sorchard001/D32MKII-Schematic/Dragon32_MKII.kicad_sch

## KiCad design Dragon32_MKII.kicad_sch (2026-08-14)

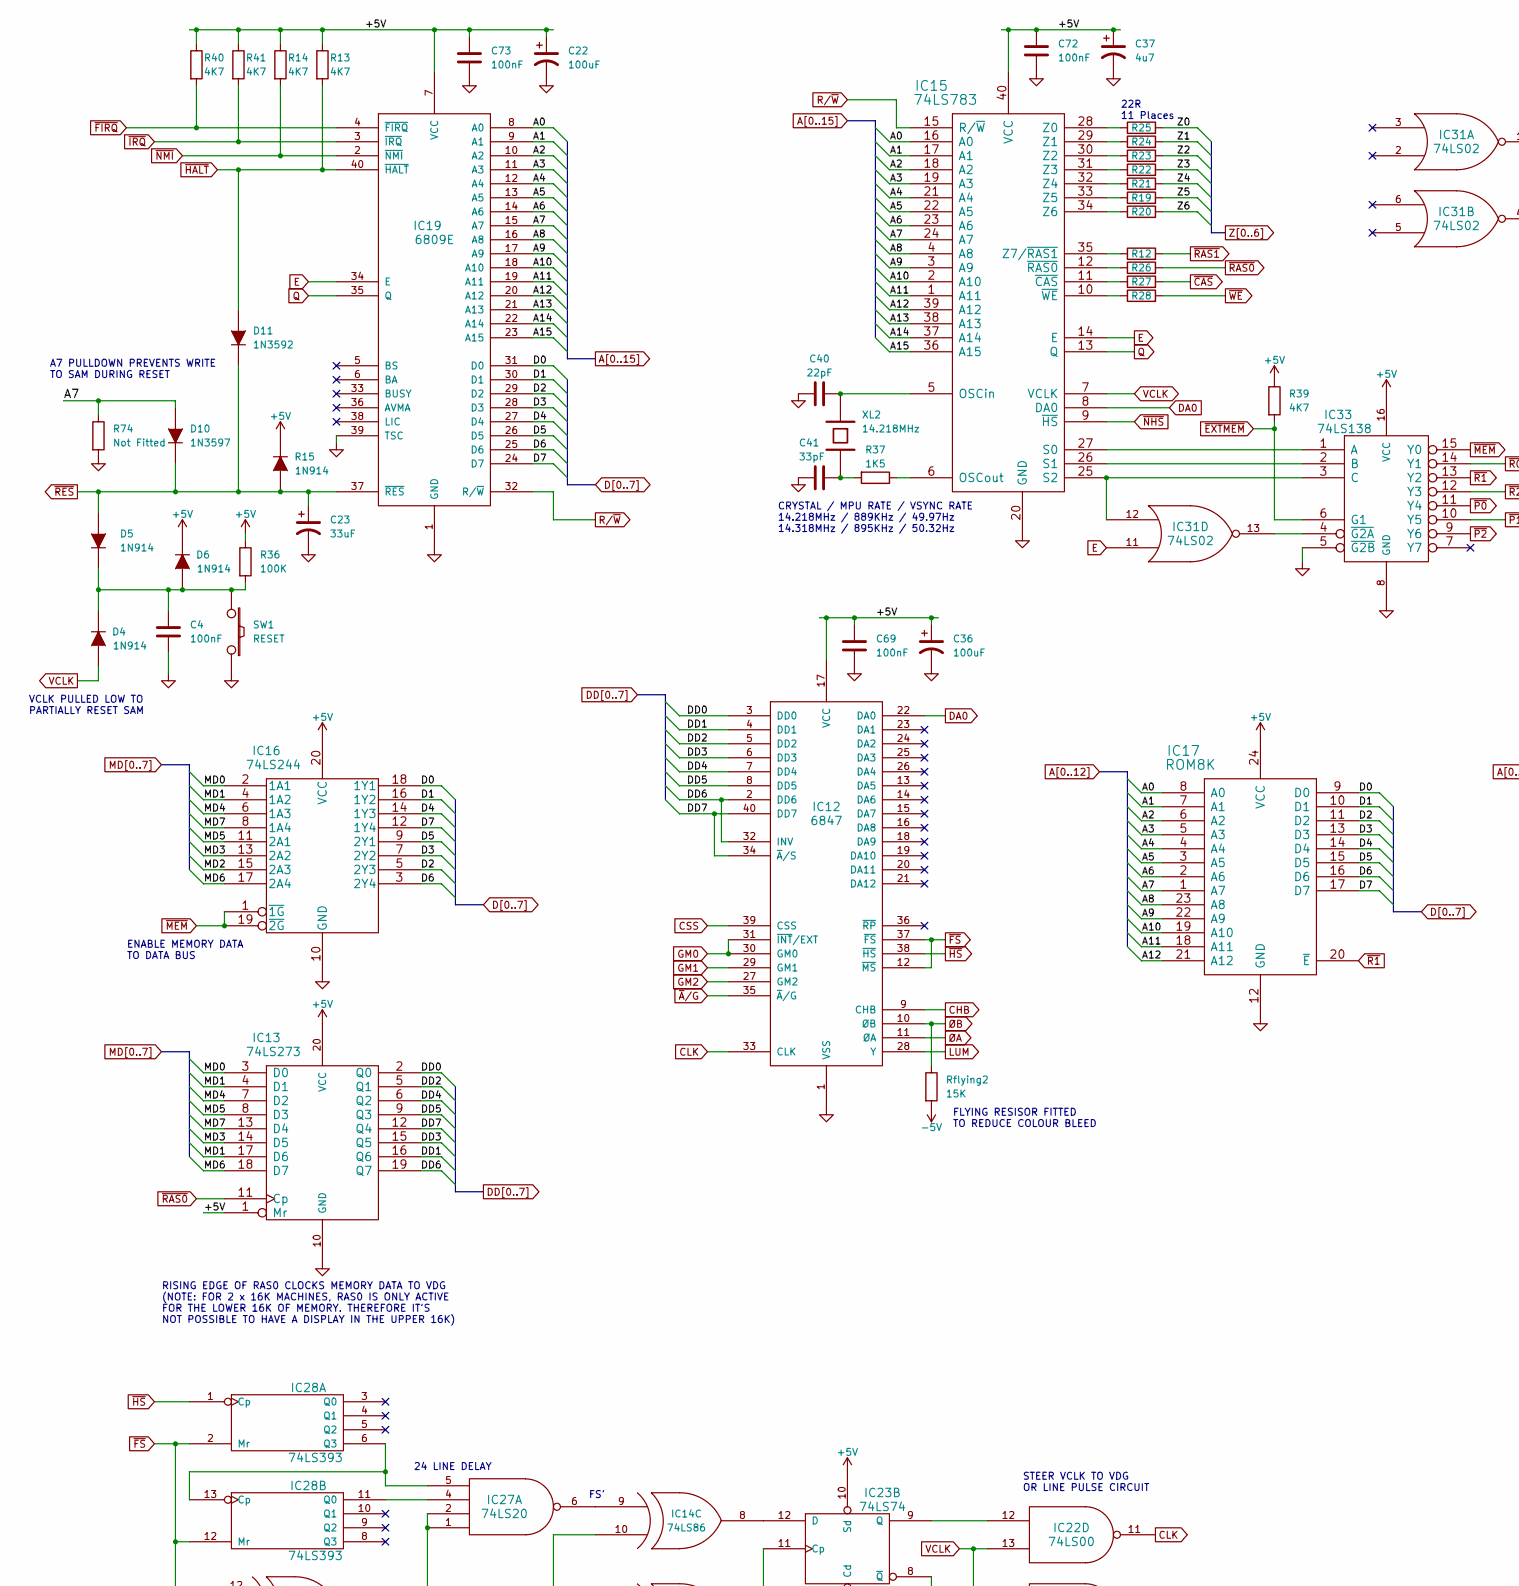
[picture p2: schematic Dragon32_MKII.kicad_sch, part in row 1, column 1]

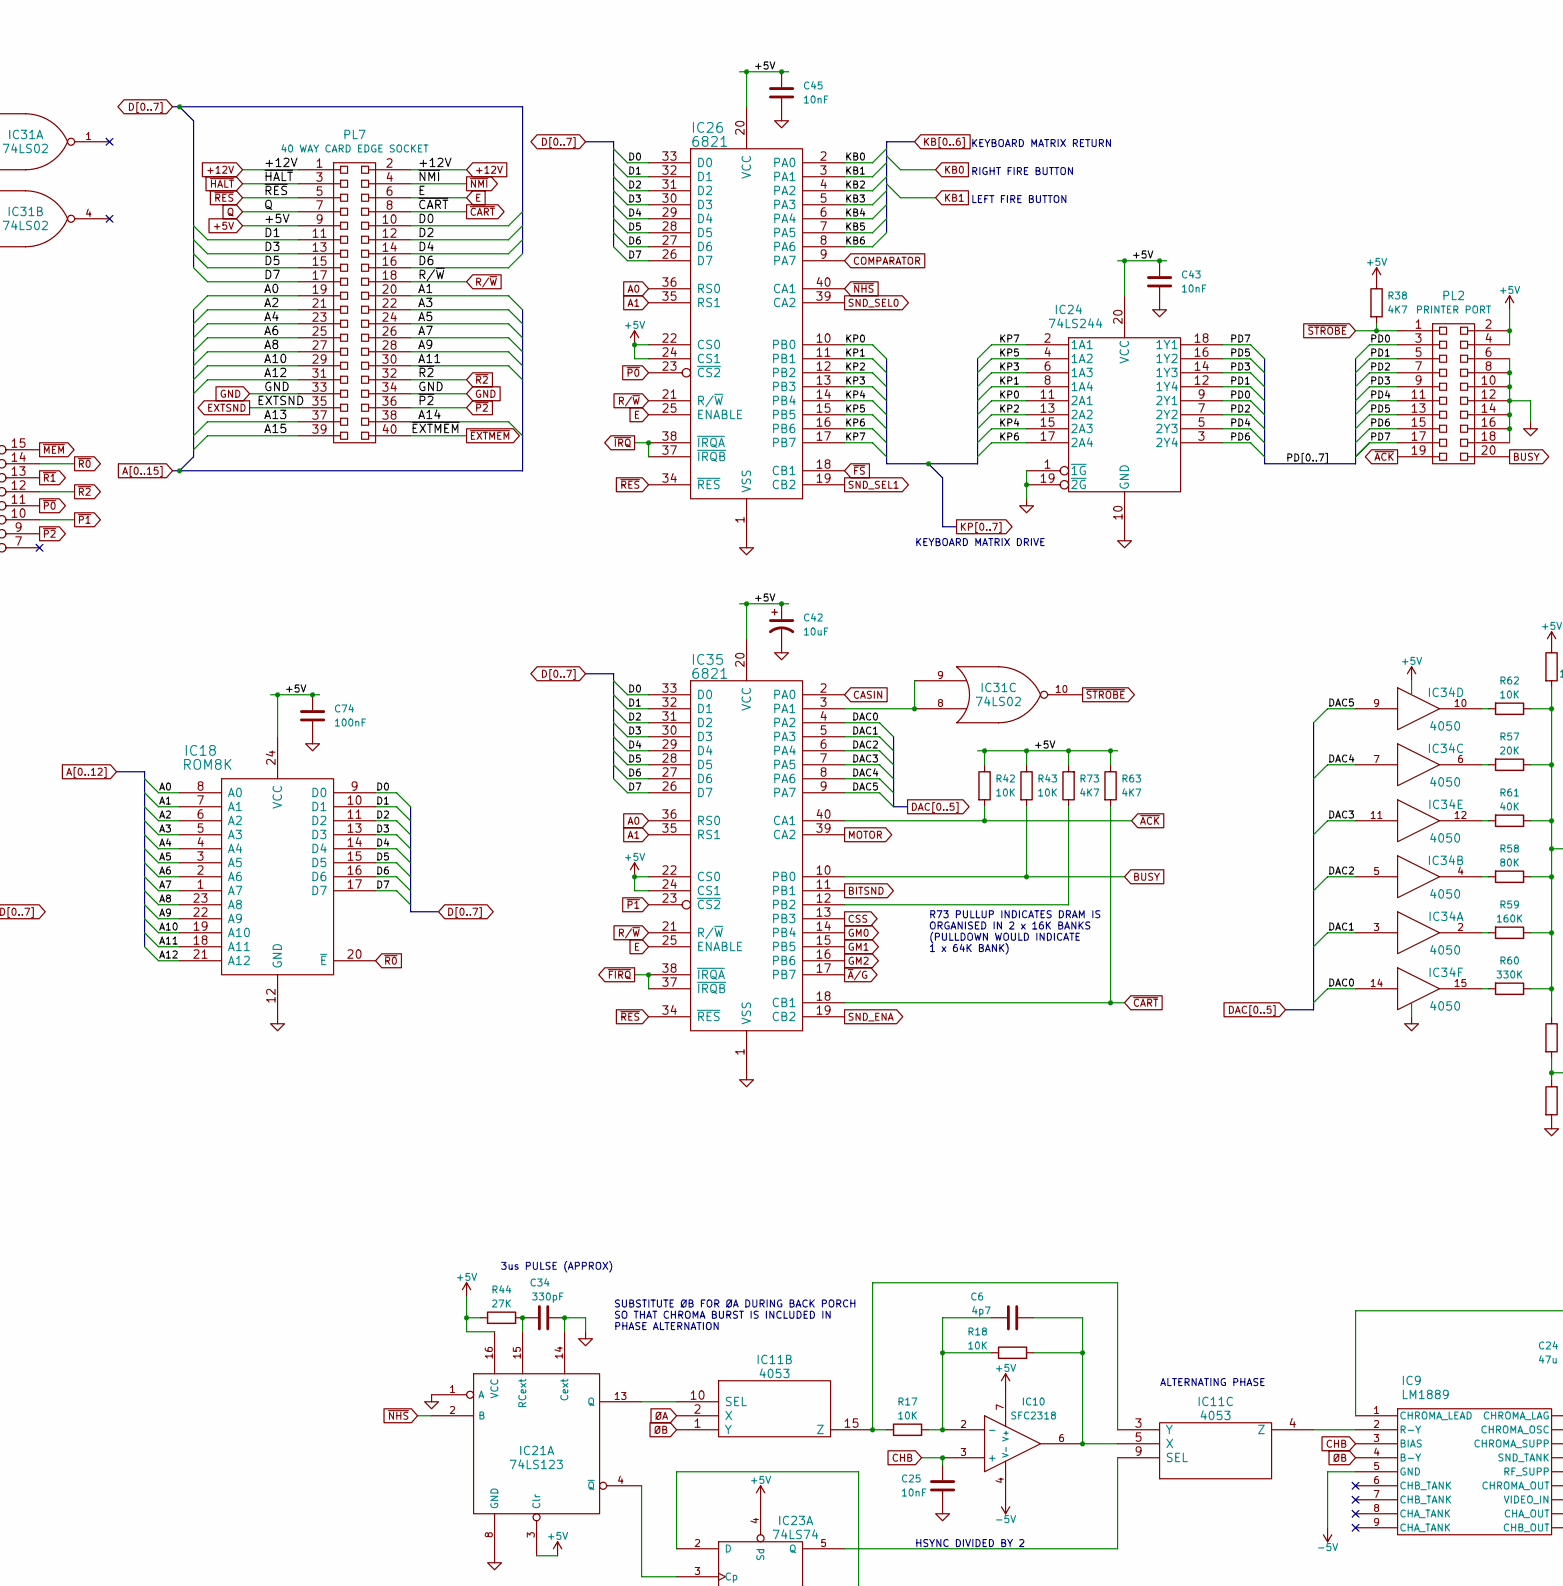
[picture p3: schematic Dragon32_MKII.kicad_sch, part in row 1, column 2]

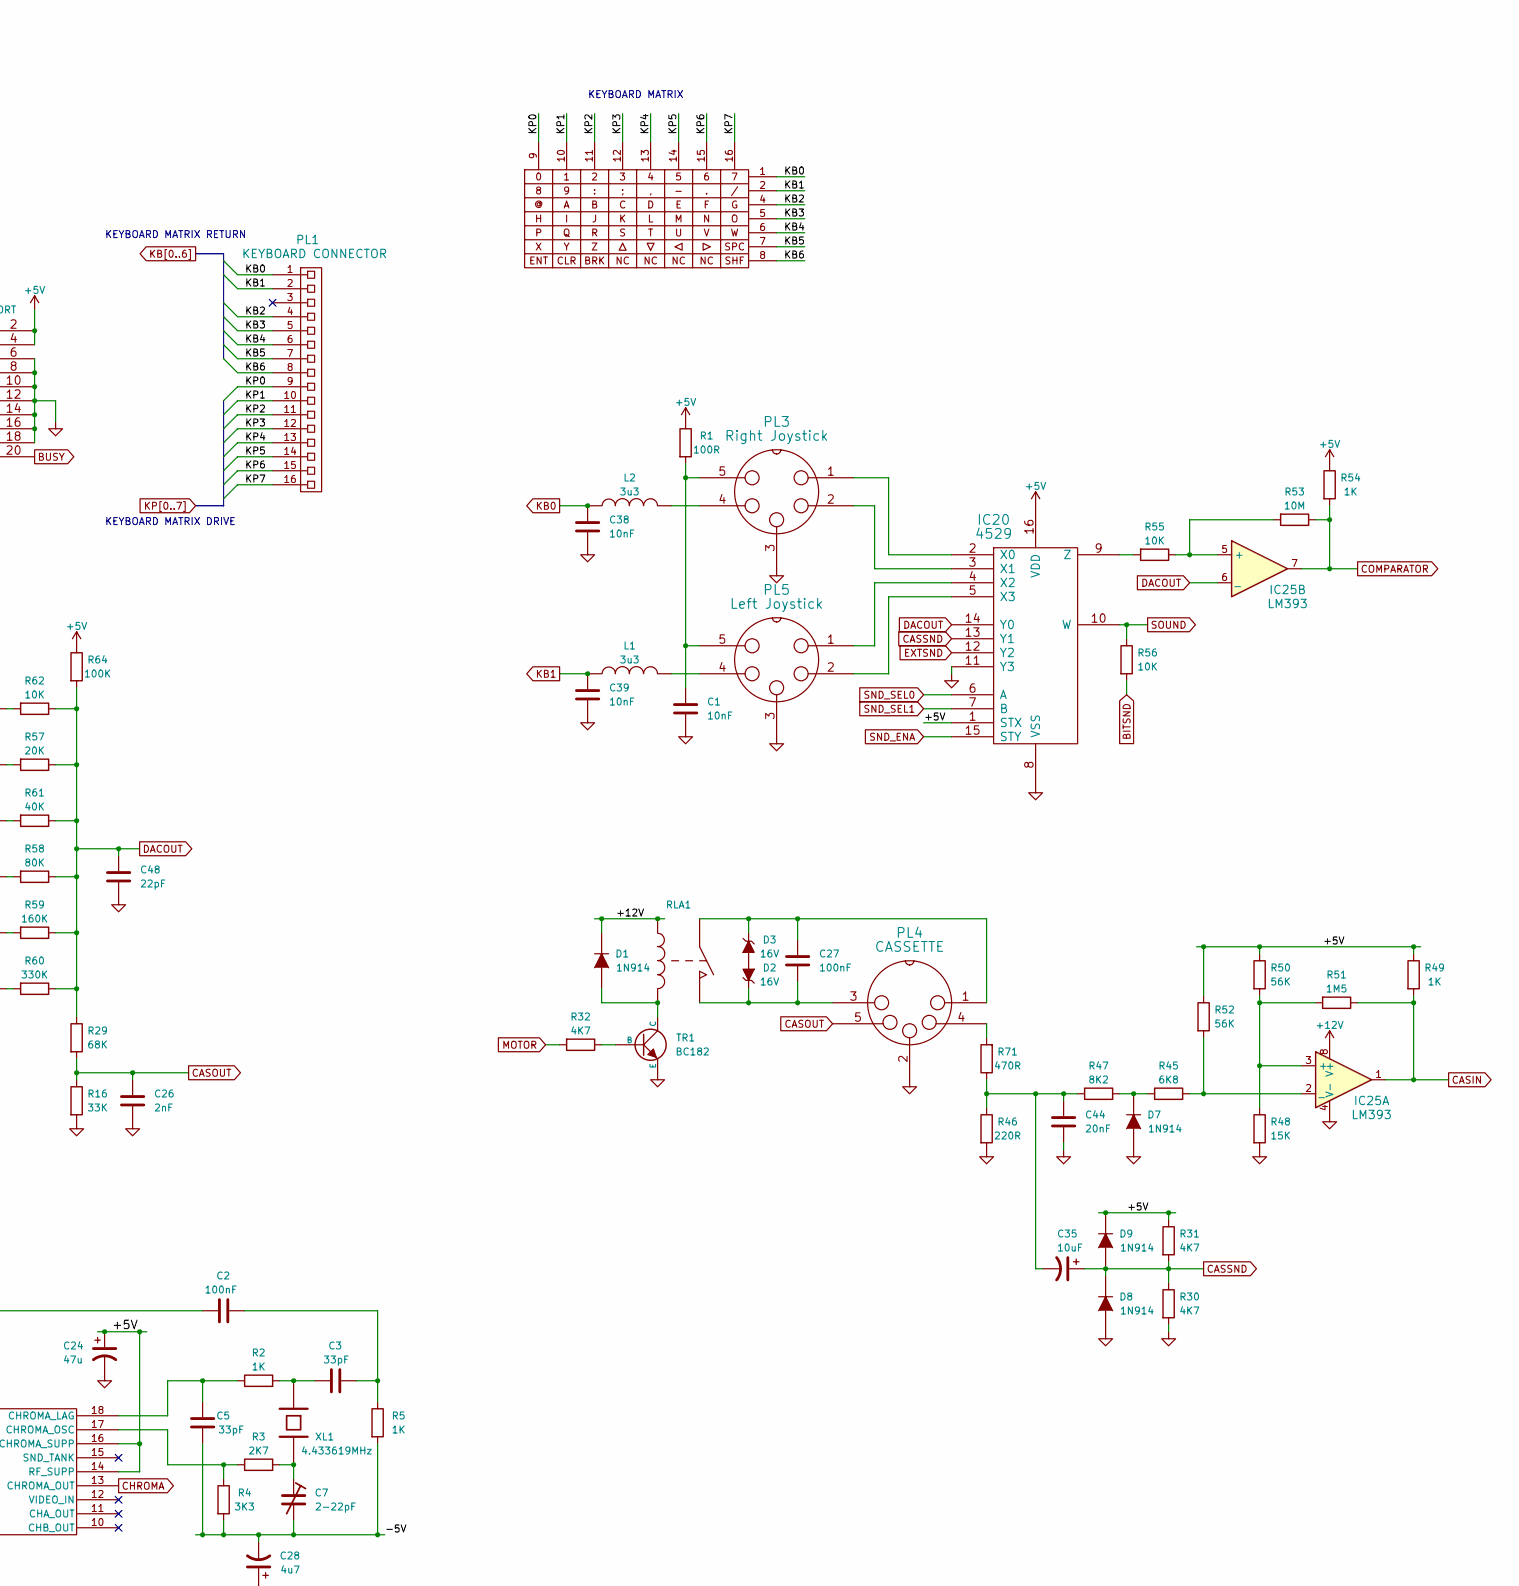
[picture p4: schematic Dragon32_MKII.kicad_sch, part in row 1, column 3]

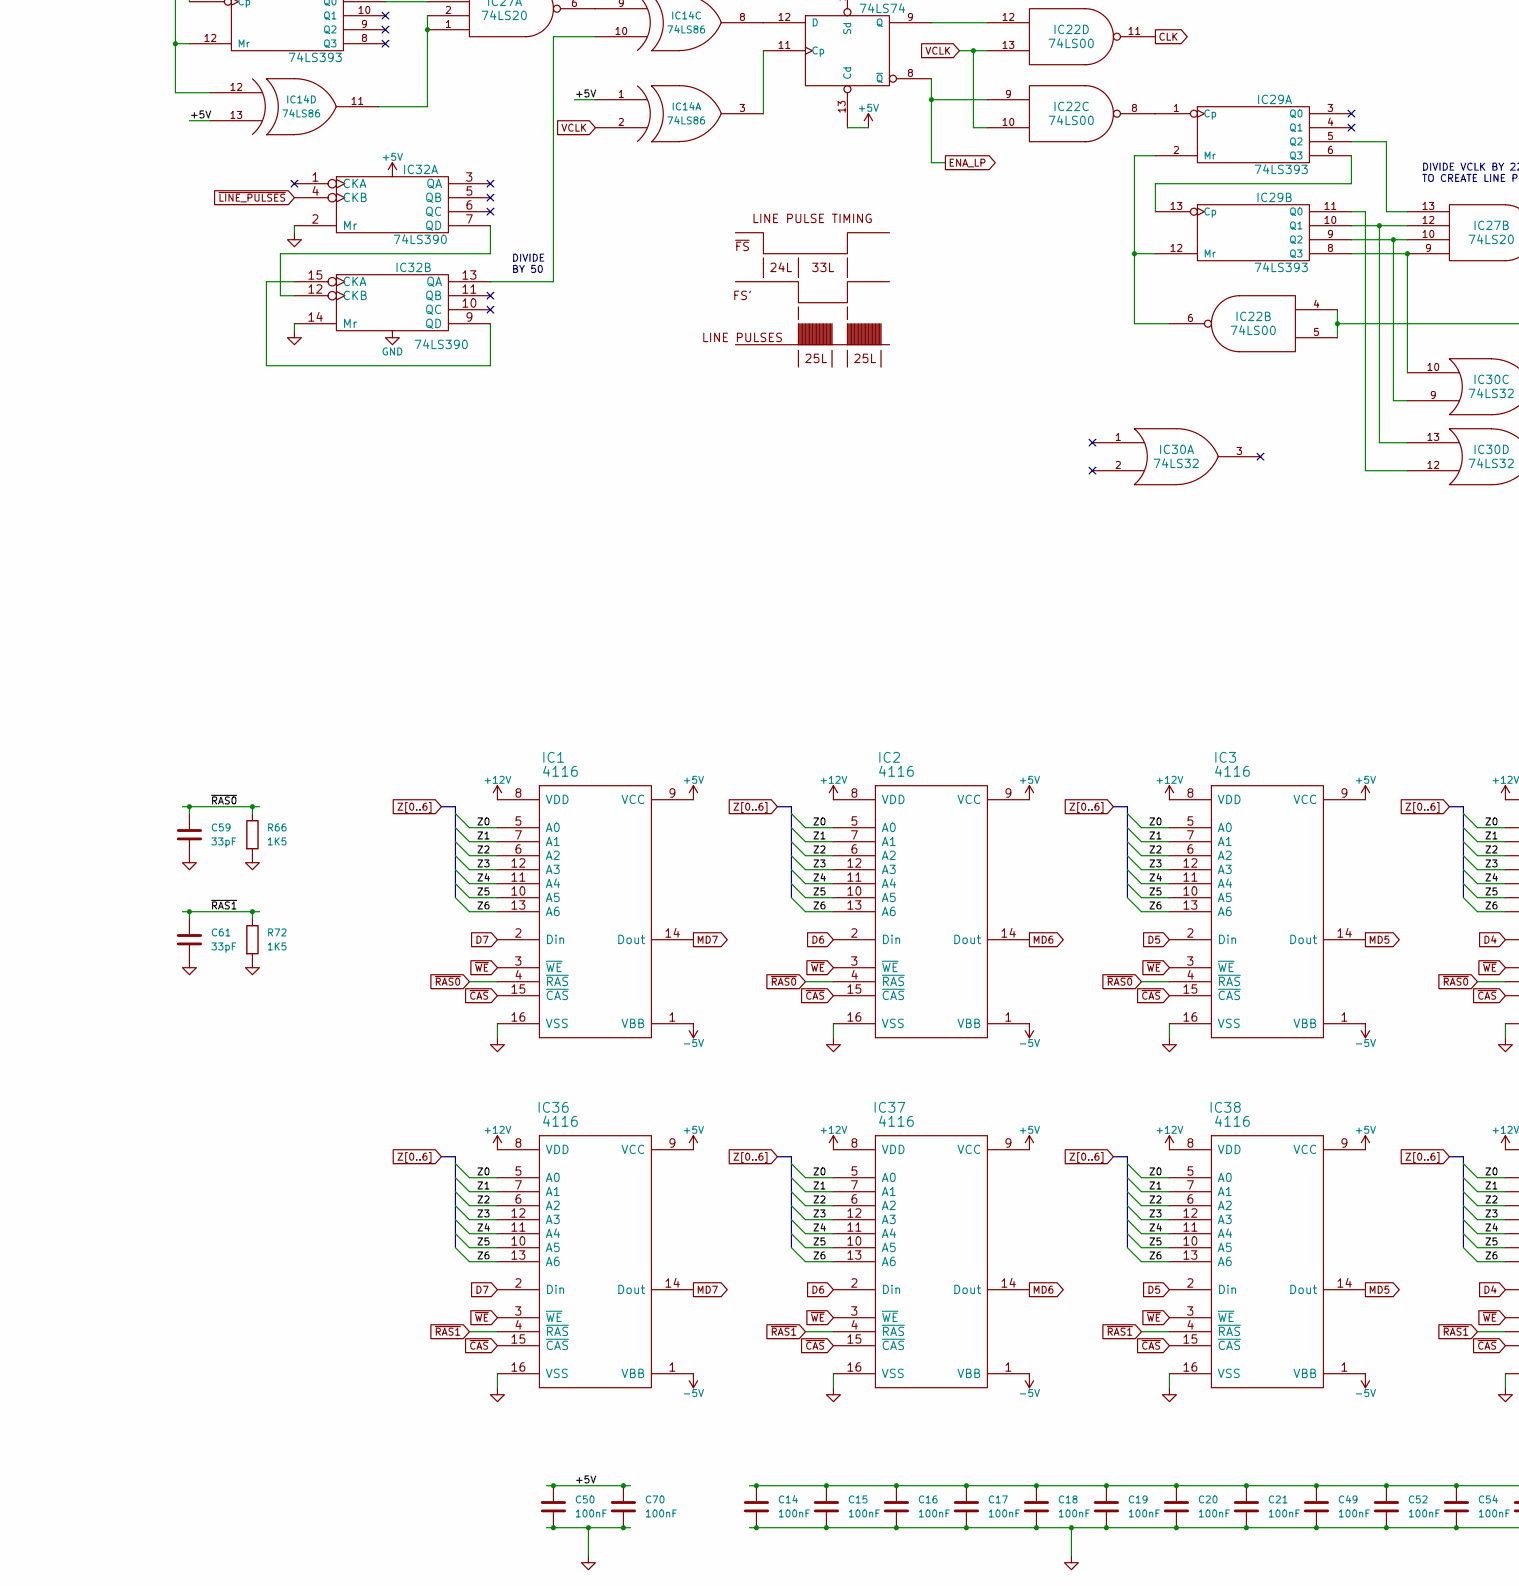
[picture p5: schematic Dragon32_MKII.kicad_sch, part in row 2, column 1]

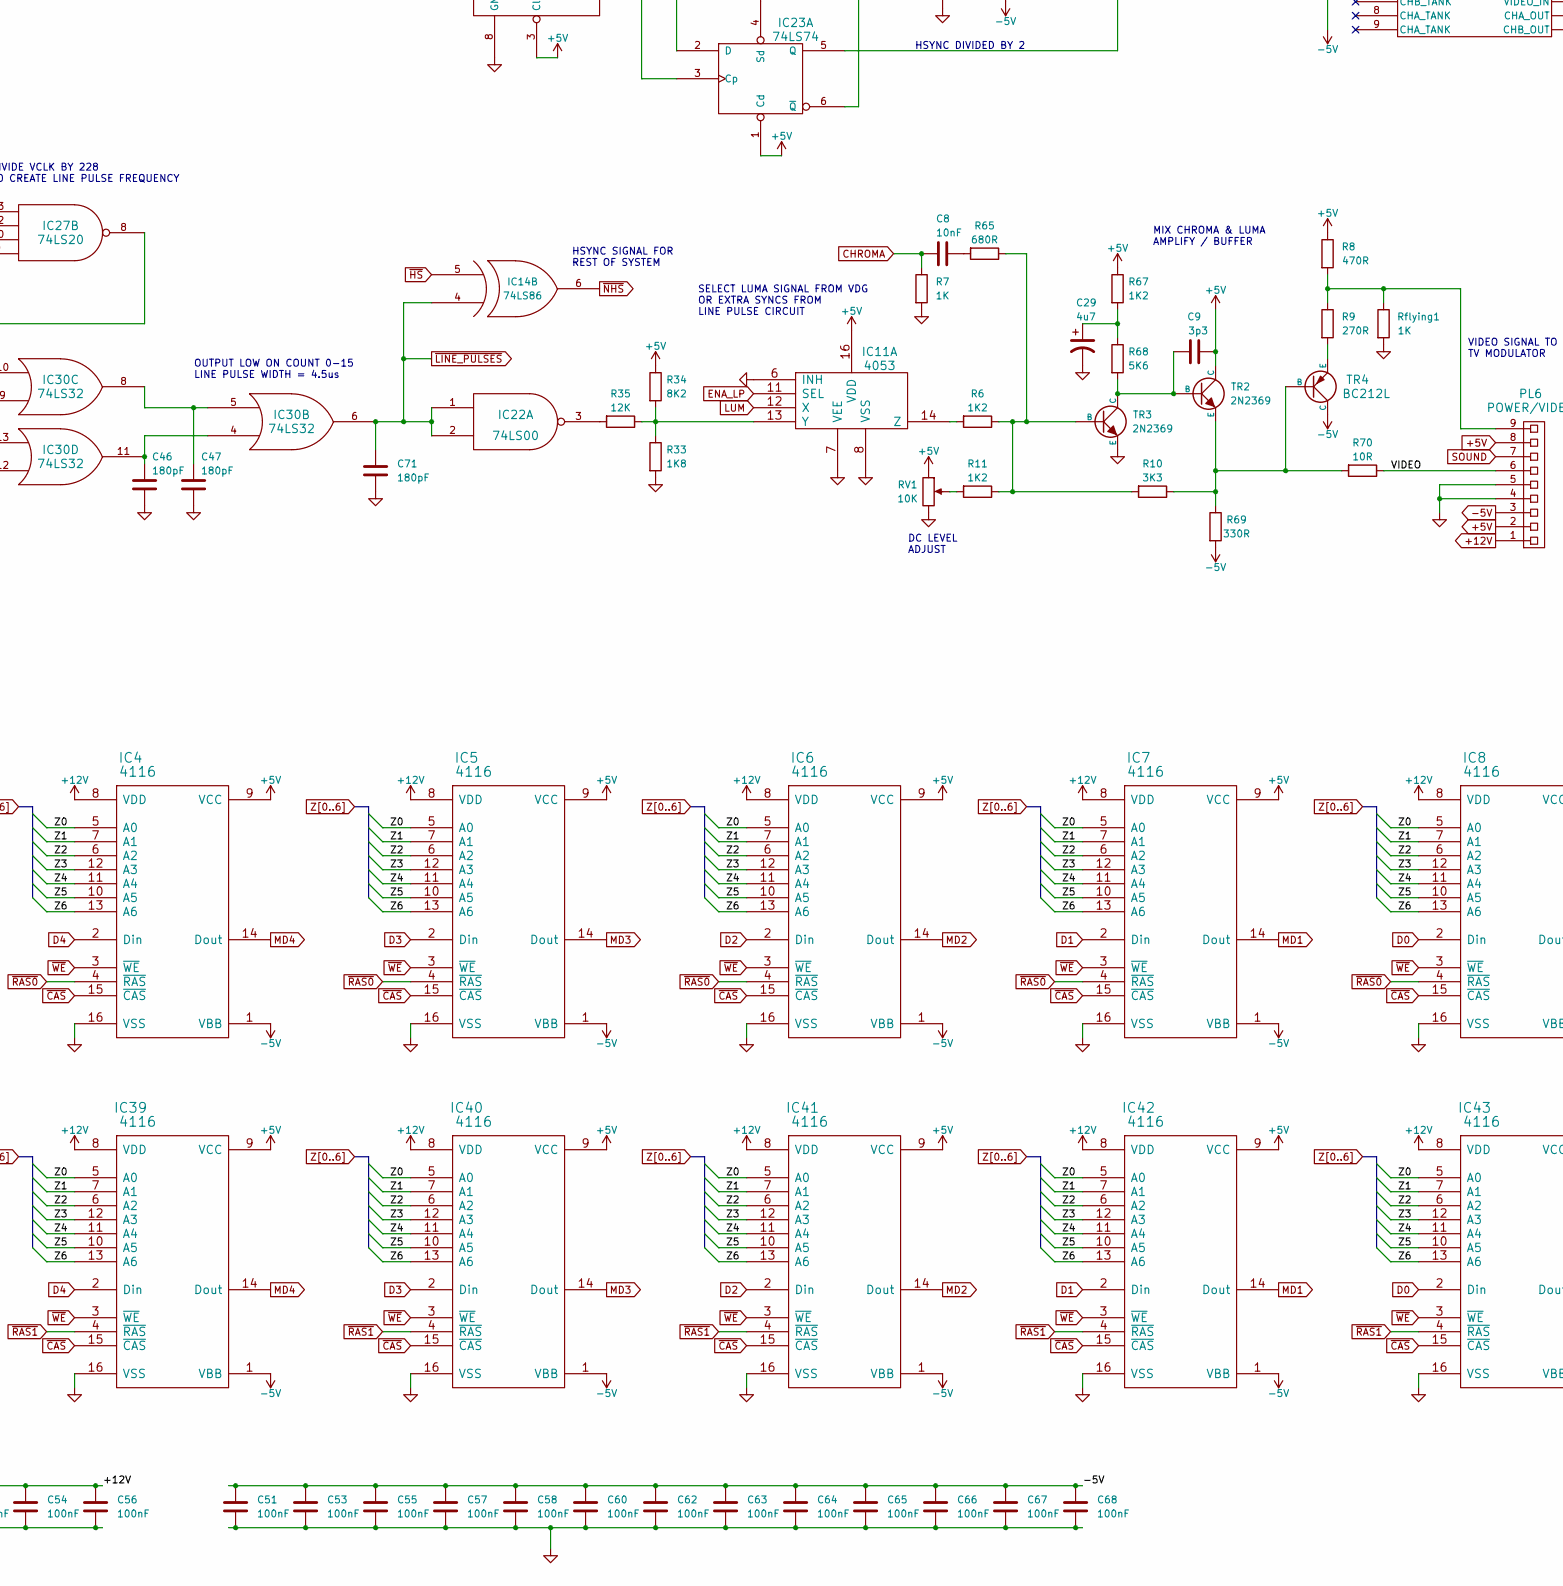
[picture p6: schematic Dragon32_MKII.kicad_sch, part in row 2, column 2]

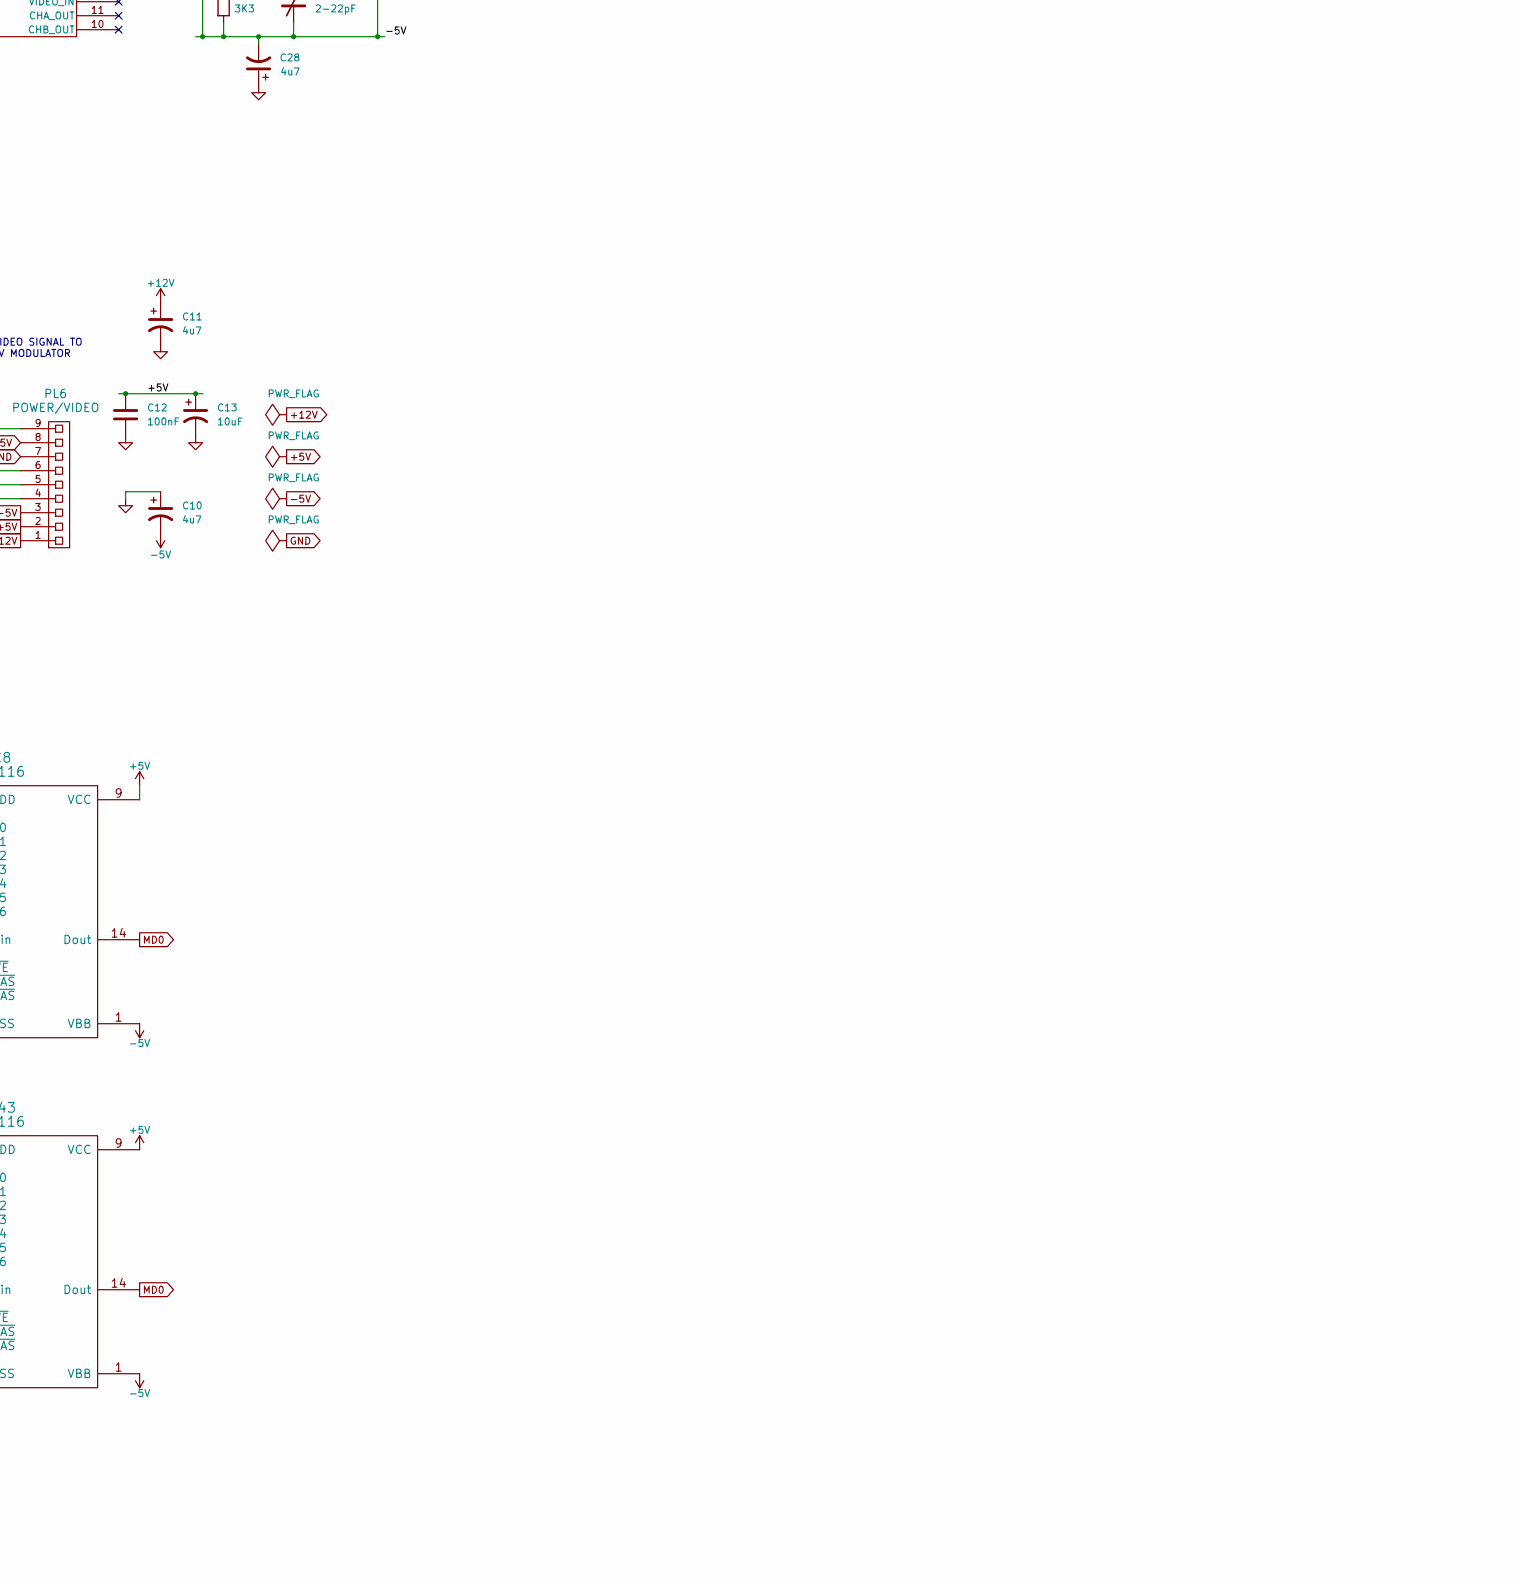
[picture p7: schematic Dragon32_MKII.kicad_sch, part in row 2, column 3]

Parts:
C1, C8, C25, C38, C39, C43, C45: 10nF
C2, C4, C12, C14, C15, C16, C17, C18, C19, C20, C21, C27, C49, C50, C51, C52, C53, C54, C55, C56, C57, C58, C60, C62, C63, C64, C65, C66, C67, C68, C69, C70, C72, C73, C74: 100nF
C3, C5, C41, C59, C61: 33pF
C6: 4p7
C7: 2-22pF
C9: 3p3
C10, C11, C28, C29, C37: 4u7
C13, C35, C42: 10uF
C22, C36: 100uF
C23: 33uF
C24: 47u
C26: 2nF
C34: 330pF
C40, C48: 22pF
C44: 20nF
C46, C47, C71: 180pF
D1, D4, D5, D6, D7, D8, D9: 1N914
D2, D3: 16V
D10: 1N3597
D11: 1N3592
IC1, IC2, IC3, IC4, IC5, IC6, IC7, IC8, IC36, IC37, IC38, IC39, IC40, IC41, IC42, IC43: 4116
IC9: LM1889
IC10: SFC2318
IC11: 4053
IC12: 6847
IC13: 74LS273
IC14: 74LS86
IC15: 74LS783
IC16, IC24: 74LS244
IC17, IC18: ROM8K
IC19: 6809E
IC20: 4529
IC21: 74LS123
IC22: 74LS00
IC23: 74LS74
IC25: LM393
IC26, IC35: 6821
IC27: 74LS20
IC28, IC29: 74LS393
IC30: 74LS32
IC31: 74LS02
IC32: 74LS390
IC33: 74LS138
IC34: 4050
L1, L2: 3u3
PL1: KEYBOARD CONNECTOR
PL2: PRINTER PORT
PL3: Right Joystick
PL4: CASSETTE
PL5: Left Joystick
PL6: POWER/VIDEO
PL7: 40 WAY CARD EDGE SOCKET
R1: 100R
R2, R5, R7, R49, R54: 1K
R3: 2K7
R4, R10: 3K3
R6, R11, R67: 1K2
R8, R71: 470R
R9: 270R
R12, R19, R20, R21, R22, R23, R24, R25, R26, R27, R28: 22R
R13, R14, R30, R31, R32, R38, R39, R40, R41, R63, R73: 4K7
R15: 1N914
R16: 33K
R17, R18, R42, R43, R55, R56, R62: 10K
R29: 68K
R33: 1K8
R34, R47: 8K2
R35: 12K
R36, R64: 100K
R37, R66, R72: 1K5
R44: 27K
R45: 6K8
R46: 220R
R48: 15K
R50, R52: 56K
R51: 1M5
R53: 10M
R57: 20K
R58: 80K
R59: 160K
R60: 330K
R61: 40K
R65: 680R
R68: 5K6
R69: 330R
R70: 10R
R74: Not Fitted
RLA1: RELAY
RV1: 10K
Rflying1: 1K
Rflying2: 15K
SW1: RESET
TR1: BC182; TO92-CBE
TR2, TR3: 2N2369
TR4: BC212L
U1: LINE_PULSE_DIAGRAM
U2: (no value)
XL1: 4.433619MHz
XL2: 14.218MHz

Connections:
+5V: C9.2, C12.1, C13.1, C22.1, C24.1, C36.1, C37.1, C42.1, C43.1, C45.1, C50.1, C69.1, C70.1, C72.1, C73.1, C74.1, D6.2 (K), D9.2 (K), IC1.9 (VCC), IC2.9 (VCC), IC3.9 (VCC), IC4.9 (VCC), IC5.9 (VCC), IC6.9 (VCC), IC7.9 (VCC), IC8.9 (VCC), IC9.14 (RF_SUPP), IC9.16 (CHROMA_SUPP), IC10.7 (V+), IC11.16 (VDD), IC12.17 (VCC), IC13.1 (Mr), IC13.20 (VCC), IC14.1 (IN1), IC14.13 (IN2), IC15.40 (VCC), IC16.20 (VCC), IC17.24 (VCC), IC18.24 (VCC), IC19.7 (VCC), IC20.1 (STX), IC20.16 (VDD), IC21.3 (Clr), IC21.16 (VCC), IC23.1 (Cd), IC23.4 (Sd), IC23.10 (Sd), IC23.13 (Cd), IC24.20 (VCC), IC26.20 (VCC), IC26.22 (CS0), IC26.24 (CS1), IC32.16 (VCC), IC33.16 (VCC), IC34.1 (VCC), IC35.20 (VCC), IC35.22 (CS0), IC35.24 (CS1), IC36.9 (VCC), IC37.9 (VCC), IC38.9 (VCC), IC39.9 (VCC), IC40.9 (VCC), IC41.9 (VCC), IC42.9 (VCC), IC43.9 (VCC), PL2.2, PL2.4, PL6.2, PL6.8, PL7.9, R1.1, R8.1, R13.1, R14.1, R15.2 (K), R31.1, R34.1, R36.1, R38.1, R39.1, R40.1, R41.1, R42.1, R43.1, R44.1, R49.1, R50.1, R52.1, R54.1, R63.1, R64.1, R67.1, R73.2, RV1.1, TR2.3 (C)
+12V: C11.1, C14.1, C15.1, C16.1, C17.1, C18.1, C19.1, C20.1, C21.1, C49.1, C52.1, C54.1, C56.1, D1.2 (K), IC1.8 (VDD), IC2.8 (VDD), IC3.8 (VDD), IC4.8 (VDD), IC5.8 (VDD), IC6.8 (VDD), IC7.8 (VDD), IC8.8 (VDD), IC25.8 (V+), IC36.8 (VDD), IC37.8 (VDD), IC38.8 (VDD), IC39.8 (VDD), IC40.8 (VDD), IC41.8 (VDD), IC42.8 (VDD), IC43.8 (VDD), PL6.1, PL7.1, PL7.2, RLA1.1
-5V: C5.1, C7.2, C10.2, C28.2, C51.1, C53.1, C55.1, C57.1, C58.1, C60.1, C62.1, C63.1, C64.1, C65.1, C66.1, C67.1, C68.1, IC1.1 (VBB), IC2.1 (VBB), IC3.1 (VBB), IC4.1 (VBB), IC5.1 (VBB), IC6.1 (VBB), IC7.1 (VBB), IC8.1 (VBB), IC9.5 (GND), IC10.4 (V-), IC36.1 (VBB), IC37.1 (VBB), IC38.1 (VBB), IC39.1 (VBB), IC40.1 (VBB), IC41.1 (VBB), IC42.1 (VBB), IC43.1 (VBB), PL6.3, R4.2, R5.2, R69.2, Rflying2.2, TR4.3 (C)
A0: IC15.16 (A0), IC17.8 (A0), IC18.8 (A0), IC19.8 (A0), IC26.36 (RS0), IC35.36 (RS0), PL7.19
A1: IC15.17 (A1), IC17.7 (A1), IC18.7 (A1), IC19.9 (A1), IC26.35 (RS1), IC35.35 (RS1), PL7.20
A2: IC15.18 (A2), IC17.6 (A2), IC18.6 (A2), IC19.10 (A2), PL7.21
A3: IC15.19 (A3), IC17.5 (A3), IC18.5 (A3), IC19.11 (A3), PL7.22
A4: IC15.21 (A4), IC17.4 (A4), IC18.4 (A4), IC19.12 (A4), PL7.23
A5: IC15.22 (A5), IC17.3 (A5), IC18.3 (A5), IC19.13 (A5), PL7.24
A6: IC15.23 (A6), IC17.2 (A6), IC18.2 (A6), IC19.14 (A6), PL7.25
A7: D10.1 (A), IC15.24 (A7), IC17.1 (A7), IC18.1 (A7), IC19.15 (A7), PL7.26, R74.1
A8: IC15.4 (A8), IC17.23 (A8), IC18.23 (A8), IC19.16 (A8), PL7.27
A9: IC15.3 (A9), IC17.22 (A9), IC18.22 (A9), IC19.17 (A9), PL7.28
A10: IC15.2 (A10), IC17.19 (A10), IC18.19 (A10), IC19.18 (A10), PL7.29
A11: IC15.1 (A11), IC17.18 (A11), IC18.18 (A11), IC19.19 (A11), PL7.30
A12: IC15.39 (A12), IC17.21 (A12), IC18.21 (A12), IC19.20 (A12), PL7.31
A13: IC15.38 (A13), IC19.21 (A13), PL7.37
A14: IC15.37 (A14), IC19.22 (A14), PL7.38
A15: IC15.36 (A15), IC19.23 (A15), PL7.39
BITSND: IC35.11 (PB1), R56.2
BUSY: IC35.10 (PB0), PL2.20, R43.2
CASIN: IC25.1, IC35.2 (PA0), R49.2, R51.1
CASOUT: C26.1, PL4.5, R16.1, R29.2
CASSND: C35.1, D8.2 (K), D9.1 (A), IC20.13 (Y1), R30.1, R31.2
CHB: C25.1, IC9.3 (BIAS), IC10.3 (+), IC12.9 (CHB)
CHROMA: C8.2, IC9.13 (CHROMA_OUT), R7.1
CLK: IC12.33 (CLK), IC22.11
COMPARATOR: IC25.7, IC26.9 (PA7), R53.1, R54.2
CSS: IC12.39 (CSS), IC35.13 (PB3)
D0: IC8.2 (Din), IC16.18 (1Y1), IC17.9 (D0), IC18.9 (D0), IC19.31 (D0), IC26.33 (D0), IC35.33 (D0), IC43.2 (Din), PL7.10
D1: IC7.2 (Din), IC16.16 (1Y2), IC17.10 (D1), IC18.10 (D1), IC19.30 (D1), IC26.32 (D1), IC35.32 (D1), IC42.2 (Din), PL7.11
D2: IC6.2 (Din), IC16.5 (2Y3), IC17.11 (D2), IC18.11 (D2), IC19.29 (D2), IC26.31 (D2), IC35.31 (D2), IC41.2 (Din), PL7.12
D3: IC5.2 (Din), IC16.7 (2Y2), IC17.13 (D3), IC18.13 (D3), IC19.28 (D3), IC26.30 (D3), IC35.30 (D3), IC40.2 (Din), PL7.13
D4: IC4.2 (Din), IC16.14 (1Y3), IC17.14 (D4), IC18.14 (D4), IC19.27 (D4), IC26.29 (D4), IC35.29 (D4), IC39.2 (Din), PL7.14
D5: IC3.2 (Din), IC16.9 (2Y1), IC17.15 (D5), IC18.15 (D5), IC19.26 (D5), IC26.28 (D5), IC35.28 (D5), IC38.2 (Din), PL7.15
D6: IC2.2 (Din), IC16.3 (2Y4), IC17.16 (D6), IC18.16 (D6), IC19.25 (D6), IC26.27 (D6), IC35.27 (D6), IC37.2 (Din), PL7.16
D7: IC1.2 (Din), IC16.12 (1Y4), IC17.17 (D7), IC18.17 (D7), IC19.24 (D7), IC26.26 (D7), IC35.26 (D7), IC36.2 (Din), PL7.17
DA0: IC12.22 (DA0), IC15.8 (DA0)
DAC0: IC34.14, IC35.4 (PA2)
DAC1: IC34.3, IC35.5 (PA3)
DAC2: IC34.5, IC35.6 (PA4)
DAC3: IC34.11, IC35.7 (PA5)
DAC4: IC34.7, IC35.8 (PA6)
DAC5: IC34.9, IC35.9 (PA7)
DACOUT: C48.1, IC20.14 (Y0), IC25.6 (_), R29.1, R57.1, R58.1, R59.1, R60.1, R61.1, R62.1, R64.2
DD0: IC12.3 (DD0), IC13.2 (Q0)
DD1: IC12.4 (DD1), IC13.16 (Q6)
DD2: IC12.5 (DD2), IC13.5 (Q1)
DD3: IC12.6 (DD3), IC13.15 (Q5)
DD4: IC12.7 (DD4), IC13.6 (Q2)
DD5: IC12.8 (DD5), IC13.9 (Q3)
DD6: IC12.2 (DD6), IC12.32 (INV), IC13.19 (Q7)
DD7: IC12.34 (~A/S), IC12.40 (DD7), IC13.12 (Q4)
E: IC15.14 (E), IC19.34 (E), IC26.25 (ENABLE), IC31.11, IC35.25 (ENABLE), PL7.6
ENA_LP: IC11.11 (SEL), IC22.9, IC23.8 (~Q)
EXTSND: IC20.12 (Y2), PL7.35
GM0: IC12.30 (GM0), IC12.31 (~INT/EXT), IC35.14 (PB4)
GM1: IC12.29 (GM1), IC35.15 (PB5)
GM2: IC12.27 (GM2), IC35.16 (PB6)
GND: C1.2, C4.2, C10.1, C11.2, C12.2, C13.2, C14.2, C15.2, C16.2, C17.2, C18.2, C19.2, C20.2, C21.2, C22.2, C23.2, C24.2, C25.2, C26.2, C28.1, C29.2, C34.2, C36.2, C37.2, C38.2, C39.2, C40.2, C41.2, C42.2, C43.2, C44.2, C45.2, C46.2, C47.2, C48.2, C49.2, C50.2, C51.2, C52.2, C53.2, C54.2, C55.2, C56.2, C57.2, C58.2, C59.2, C60.2, C61.2, C62.2, C63.2, C64.2, C65.2, C66.2, C67.2, C68.2, C69.2, C70.2, C71.2, C72.2, C73.2, C74.2, D7.1 (A), D8.1 (A), IC1.16 (VSS), IC2.16 (VSS), IC3.16 (VSS), IC4.16 (VSS), IC5.16 (VSS), IC6.16 (VSS), IC7.16 (VSS), IC8.16 (VSS), IC11.6 (INH), IC11.7 (VEE), IC11.8 (VSS), IC12.1 (VSS), IC13.10 (GND), IC15.20 (GND), IC16.10 (GND), IC17.12 (GND), IC18.12 (GND), IC19.1 (GND), IC19.39 (TSC), IC20.8 (VSS), IC20.11 (Y3), IC21.1 (A), IC21.8 (GND), IC21.14 (Cext), IC24.1 (~1G), IC24.10 (GND), IC24.19 (~2G), IC25.4 (V-), IC26.1 (VSS), IC32.2 (Mr), IC32.8 (GND), IC32.14 (Mr), IC33.5 (~G2B), IC33.8 (GND), IC34.8 (VSS), IC35.1 (VSS), IC36.16 (VSS), IC37.16 (VSS), IC38.16 (VSS), IC39.16 (VSS), IC40.16 (VSS), IC41.16 (VSS), IC42.16 (VSS), IC43.16 (VSS), PL2.6, PL2.8, PL2.10, PL2.12, PL2.14, PL2.16, PL2.18, PL3.3, PL4.2, PL5.3, PL6.4, PL6.5, PL7.33, PL7.34, R7.2, R16.2, R30.2, R33.2, R46.2, R48.2, R66.2, R72.2, R74.2, RV1.3, Rflying1.2, SW1.1, TR1.3 (E), TR3.1 (E)
KB0: C38.1, IC26.2 (PA0), L2.1, PL1.1, U2.1
KB1: C39.1, IC26.3 (PA1), L1.1, PL1.2, U2.2
KB2: IC26.4 (PA2), PL1.4, U2.4
KB3: IC26.5 (PA3), PL1.5, U2.5
KB4: IC26.6 (PA4), PL1.6, U2.6
KB5: IC26.7 (PA5), PL1.7, U2.7
KB6: IC26.8 (PA6), PL1.8, U2.8
KP0: IC24.11 (2A1), IC26.10 (PB0), PL1.9, U2.9
KP1: IC24.8 (1A4), IC26.11 (PB1), PL1.10, U2.10
KP2: IC24.13 (2A2), IC26.12 (PB2), PL1.11, U2.11
KP3: IC24.6 (1A3), IC26.13 (PB3), PL1.12, U2.12
KP4: IC24.15 (2A3), IC26.14 (PB4), PL1.13, U2.13
KP5: IC24.4 (1A2), IC26.15 (PB5), PL1.14, U2.14
KP6: IC24.17 (2A4), IC26.16 (PB6), PL1.15, U2.15
KP7: IC24.2 (1A1), IC26.17 (PB7), PL1.16, U2.16
LUM: IC11.12 (X), IC12.28 (Y)
MD0: IC8.14 (Dout), IC13.3 (D0), IC16.2 (1A1), IC43.14 (Dout)
MD1: IC7.14 (Dout), IC13.4 (D1), IC13.17 (D6), IC16.4 (1A2), IC42.14 (Dout)
MD2: IC6.14 (Dout), IC16.15 (2A3), IC41.14 (Dout)
MD3: IC5.14 (Dout), IC13.14 (D5), IC16.13 (2A2), IC40.14 (Dout)
MD4: IC4.14 (Dout), IC13.7 (D2), IC16.6 (1A3), IC39.14 (Dout)
MD5: IC3.14 (Dout), IC13.8 (D3), IC16.11 (2A1), IC38.14 (Dout)
MD6: IC2.14 (Dout), IC13.18 (D7), IC16.17 (2A4), IC37.14 (Dout)
MD7: IC1.14 (Dout), IC13.13 (D4), IC16.8 (1A4), IC36.14 (Dout)
MOTOR: IC35.39 (CA2), R32.2
unnamed: C1.1, PL3.5, PL5.5, R1.2
unnamed: C2.1, IC9.1 (CHROMA_LEAD)
unnamed: C2.2, C3.2, R5.1
unnamed: C3.1, R2.2, XL1.1
unnamed: C4.1, D4.2 (K), D5.2 (K), D6.1 (A), R36.2, SW1.2
unnamed: C5.2, IC9.18 (CHROMA_LAG), R2.1
unnamed: C6.1, IC10.2 (-), R17.2, R18.1
unnamed: C6.2, IC10.6, IC11.5 (X), R18.2
unnamed: C7.1, R3.2, XL1.2
unnamed: C8.1, R65.2
unnamed: C9.1, R68.2, TR2.2 (B), TR3.3 (C)
unnamed: C27.1, D3.2 (K), PL4.1, RLA1.3
unnamed: C27.2, D2.2 (K), PL4.3, RLA1.4
unnamed: C29.1, R67.2, R68.1
unnamed: C34.1, IC21.15 (RCext), R44.2
unnamed: C35.2, C44.1, R46.1, R47.1, R71.1
unnamed: C40.1, IC15.5 (OSCin), XL2.1
unnamed: C41.1, R37.2, XL2.2
unnamed: C46.1, IC30.4, IC30.11
unnamed: C47.1, IC30.5, IC30.8
unnamed: D1.1 (A), RLA1.2, TR1.1 (C)
unnamed: D2.1 (A), D3.1 (A)
unnamed: D7.2 (K), R45.1, R47.2
unnamed: IC9.17 (CHROMA_OSC), R3.1, R4.1
unnamed: IC9.2 (R-Y), IC11.4 (Z)
unnamed: IC11.9 (SEL), IC23.5 (Q)
unnamed: IC11.10 (SEL), IC21.13 (Q)
unnamed: IC11.13 (Y), R33.1, R34.2, R35.1
unnamed: IC11.14 (Z), R6.2
unnamed: IC11.3 (Y), IC11.15 (Z), R17.1
unnamed: IC14.3 (OUT), IC23.11 (Cp)
unnamed: IC14.8 (OUT), IC23.12 (D)
unnamed: IC14.9 (IN1), IC27.6
unnamed: IC14.10 (IN2), IC32.13 (QA)
unnamed: IC14.11 (OUT), IC27.1, IC27.2
unnamed: IC15.6 (OSCout), R37.1
unnamed: IC15.10 (~WE), R28.1
unnamed: IC15.11 (~CAS), R27.1
unnamed: IC15.12 (~RAS0), R26.1
unnamed: IC15.25 (S2), IC31.12, IC33.3 (C)
unnamed: IC15.26 (S1), IC33.2 (B)
unnamed: IC15.27 (S0), IC33.1 (A)
unnamed: IC15.28 (Z0), R25.1
unnamed: IC15.29 (Z1), R24.1
unnamed: IC15.30 (Z2), R23.1
unnamed: IC15.31 (Z3), R22.1
unnamed: IC15.32 (Z4), R21.1
unnamed: IC15.33 (Z5), R19.1
unnamed: IC15.34 (Z6), R20.1
unnamed: IC15.35 (Z7/~RAS1), R12.1
unnamed: IC20.2 (X0), PL3.1
unnamed: IC20.3 (X1), PL3.2
unnamed: IC20.4 (X2), PL5.1
unnamed: IC20.5 (X3), PL5.2
unnamed: IC20.9 (Z), R55.2
unnamed: IC21.4 (~Q), IC23.3 (Cp)
unnamed: IC22.3, R35.2
unnamed: IC22.4, IC22.5, IC27.8
unnamed: IC22.6, IC29.2 (Mr), IC29.12 (Mr)
unnamed: IC22.8, IC29.1 (Cp)
unnamed: IC22.12, IC23.9 (Q)
unnamed: IC23.2 (D), IC23.6 (~Q)
unnamed: IC25.2 (_), R45.2, R52.2
unnamed: IC25.3 (+), R48.1, R50.2, R51.2
unnamed: IC25.5 (+), R53.2, R55.1
unnamed: IC27.4, IC28.11 (Q0)
unnamed: IC27.5, IC28.6 (Q3), IC28.13 (Cp)
unnamed: IC27.9, IC29.8 (Q3), IC30.10
unnamed: IC27.10, IC29.9 (Q2), IC30.9
unnamed: IC27.12, IC29.10 (Q1), IC30.13
unnamed: IC27.13, IC29.5 (Q2)
unnamed: IC29.11 (Q0), IC30.12
unnamed: IC29.6 (Q3), IC29.13 (Cp)
unnamed: IC31.8, IC31.9, IC35.3 (PA1)
unnamed: IC31.13, IC33.4 (~G2A)
unnamed: IC32.7 (QD), IC32.12 (CKB)
unnamed: IC32.9 (QD), IC32.15 (CKA)
unnamed: IC34.2, R59.2
unnamed: IC34.4, R58.2
unnamed: IC34.6, R57.2
unnamed: IC34.10, R62.2
unnamed: IC34.12, R61.2
unnamed: IC34.15, R60.2
unnamed: IC35.12 (PB2), R73.1
unnamed: L1.2, PL5.4
unnamed: L2.2, PL3.4
unnamed: PL4.4, R71.2
unnamed: PL6.9, R8.2, R9.1, Rflying1.1
unnamed: R9.2, TR4.1 (E)
unnamed: R10.1, R69.1, R70.2, TR2.1 (E), TR4.2 (B)
unnamed: R6.1, R10.2, R11.1, R65.1, TR3.2 (B)
unnamed: R11.2, RV1.2
unnamed: R32.1, TR1.2 (B)
PD0: IC24.9 (2Y1), PL2.3
PD1: IC24.12 (1Y4), PL2.5
PD2: IC24.7 (2Y2), PL2.7
PD3: IC24.14 (1Y3), PL2.9
PD4: IC24.5 (2Y3), PL2.11
PD5: IC24.16 (1Y2), PL2.13
PD6: IC24.3 (2Y4), PL2.15
PD7: IC24.18 (1Y1), PL2.17
Q: IC15.13 (Q), IC19.35 (Q), PL7.7
R/~W: IC15.15 (R/~W), IC19.32 (R/~W), IC26.21 (R/~W), IC35.21 (R/~W), PL7.18
SND_ENA: IC20.15 (STY), IC35.19 (CB2)
SND_SEL0: IC20.6 (A), IC26.39 (CA2)
SND_SEL1: IC20.7 (B), IC26.19 (CB2)
SOUND: IC20.10 (W), PL6.7, R56.1
VCLK: D4.1 (A), IC14.2 (IN2), IC15.7 (VCLK), IC22.10, IC22.13
VIDEO: PL6.6, R70.1
Z0: IC1.5 (A0), IC2.5 (A0), IC3.5 (A0), IC4.5 (A0), IC5.5 (A0), IC6.5 (A0), IC7.5 (A0), IC8.5 (A0), IC36.5 (A0), IC37.5 (A0), IC38.5 (A0), IC39.5 (A0), IC40.5 (A0), IC41.5 (A0), IC42.5 (A0), IC43.5 (A0), R25.2
Z1: IC1.7 (A1), IC2.7 (A1), IC3.7 (A1), IC4.7 (A1), IC5.7 (A1), IC6.7 (A1), IC7.7 (A1), IC8.7 (A1), IC36.7 (A1), IC37.7 (A1), IC38.7 (A1), IC39.7 (A1), IC40.7 (A1), IC41.7 (A1), IC42.7 (A1), IC43.7 (A1), R24.2
Z2: IC1.6 (A2), IC2.6 (A2), IC3.6 (A2), IC4.6 (A2), IC5.6 (A2), IC6.6 (A2), IC7.6 (A2), IC8.6 (A2), IC36.6 (A2), IC37.6 (A2), IC38.6 (A2), IC39.6 (A2), IC40.6 (A2), IC41.6 (A2), IC42.6 (A2), IC43.6 (A2), R23.2
Z3: IC1.12 (A3), IC2.12 (A3), IC3.12 (A3), IC4.12 (A3), IC5.12 (A3), IC6.12 (A3), IC7.12 (A3), IC8.12 (A3), IC36.12 (A3), IC37.12 (A3), IC38.12 (A3), IC39.12 (A3), IC40.12 (A3), IC41.12 (A3), IC42.12 (A3), IC43.12 (A3), R22.2
Z4: IC1.11 (A4), IC2.11 (A4), IC3.11 (A4), IC4.11 (A4), IC5.11 (A4), IC6.11 (A4), IC7.11 (A4), IC8.11 (A4), IC36.11 (A4), IC37.11 (A4), IC38.11 (A4), IC39.11 (A4), IC40.11 (A4), IC41.11 (A4), IC42.11 (A4), IC43.11 (A4), R21.2
Z5: IC1.10 (A5), IC2.10 (A5), IC3.10 (A5), IC4.10 (A5), IC5.10 (A5), IC6.10 (A5), IC7.10 (A5), IC8.10 (A5), IC36.10 (A5), IC37.10 (A5), IC38.10 (A5), IC39.10 (A5), IC40.10 (A5), IC41.10 (A5), IC42.10 (A5), IC43.10 (A5), R19.2
Z6: IC1.13 (A6), IC2.13 (A6), IC3.13 (A6), IC4.13 (A6), IC5.13 (A6), IC6.13 (A6), IC7.13 (A6), IC8.13 (A6), IC36.13 (A6), IC37.13 (A6), IC38.13 (A6), IC39.13 (A6), IC40.13 (A6), IC41.13 (A6), IC42.13 (A6), IC43.13 (A6), R20.2
~ACK: IC35.40 (CA1), PL2.19, R42.2
~A/G: IC12.35 (~A/G), IC35.17 (PB7)
~CART: IC35.18 (CB1), PL7.8, R63.2
~CAS: IC1.15 (~CAS), IC2.15 (~CAS), IC3.15 (~CAS), IC4.15 (~CAS), IC5.15 (~CAS), IC6.15 (~CAS), IC7.15 (~CAS), IC8.15 (~CAS), IC36.15 (~CAS), IC37.15 (~CAS), IC38.15 (~CAS), IC39.15 (~CAS), IC40.15 (~CAS), IC41.15 (~CAS), IC42.15 (~CAS), IC43.15 (~CAS), R27.2
~EXTMEM: IC33.6 (G1), PL7.40, R39.2
~FIRQ: IC19.4 (~FIRQ), IC35.37 (~IRQB), IC35.38 (~IRQA), R40.2
~FS: IC12.12 (~MS), IC12.37 (~FS), IC14.12 (IN1), IC26.18 (CB1), IC28.2 (Mr), IC28.12 (Mr)
~HALT: D11.1 (A), IC19.40 (~HALT), PL7.3, R13.2
~HS: IC12.38 (~HS), IC14.5 (IN2), IC28.1 (Cp)
~IRQ: IC19.3 (~IRQ), IC26.37 (~IRQB), IC26.38 (~IRQA), R41.2
~LINE_PULSES: C71.1, IC14.4 (IN1), IC22.1, IC22.2, IC30.6, IC32.4 (CKB)
~MEM: IC16.1 (~1G), IC16.19 (~2G), IC33.15 (Y0)
~NHS: IC14.6 (OUT), IC15.9 (~HS), IC21.2 (B), IC26.40 (CA1)
~NMI: IC19.2 (~NMI), PL7.4, R14.2
~P0: IC26.23 (~CS2), IC33.11 (Y4)
~P1: IC33.10 (Y5), IC35.23 (~CS2)
~P2: IC33.9 (Y6), PL7.36
~R0: IC18.20 (~E), IC33.14 (Y1)
~R1: IC17.20 (~E), IC33.13 (Y2)
~R2: IC33.12 (Y3), PL7.32
~RAS0: C59.1, IC1.4 (~RAS), IC2.4 (~RAS), IC3.4 (~RAS), IC4.4 (~RAS), IC5.4 (~RAS), IC6.4 (~RAS), IC7.4 (~RAS), IC8.4 (~RAS), IC13.11 (Cp), R26.2, R66.1
~RAS1: C61.1, IC36.4 (~RAS), IC37.4 (~RAS), IC38.4 (~RAS), IC39.4 (~RAS), IC40.4 (~RAS), IC41.4 (~RAS), IC42.4 (~RAS), IC43.4 (~RAS), R12.2, R72.1
~RES: C23.1, D5.1 (A), D10.2 (K), D11.2 (K), IC19.37 (~RES), IC26.34 (~RES), IC35.34 (~RES), PL7.5, R15.1 (A)
~STROBE: IC31.10, PL2.1, R38.2
~WE: IC1.3 (~WE), IC2.3 (~WE), IC3.3 (~WE), IC4.3 (~WE), IC5.3 (~WE), IC6.3 (~WE), IC7.3 (~WE), IC8.3 (~WE), IC36.3 (~WE), IC37.3 (~WE), IC38.3 (~WE), IC39.3 (~WE), IC40.3 (~WE), IC41.3 (~WE), IC42.3 (~WE), IC43.3 (~WE), R28.2
ØA: IC11.2 (X), IC12.11 (ØA)
ØB: IC9.4 (B-Y), IC11.1 (Y), IC12.10 (ØB), Rflying2.1

Notes on the sheet:
HSYNC DIVIDED BY 2
VIDEO SIGNAL TO TV MODULATOR
RISING EDGE OF RAS0 CLOCKS MEMORY DATA TO VDG (NOTE: FOR 2 x 16K MACHINES, RAS0 IS ONLY ACTIVE FOR THE LOWER 16K OF MEMORY. THEREFORE IT'S NOT POSSIBLE TO HAVE A DISPLAY IN THE UPPER 16K)
KEYBOARD MATRIX
22R 11 Places
VCLK PULLED LOW TO PARTIALLY RESET SAM
STEER VCLK TO VDG OR LINE PULSE CIRCUIT
ENABLE MEMORY DATA TO DATA BUS
SUBSTITUTE ØB FOR ØA DURING BACK PORCH SO THAT CHROMA BURST IS INCLUDED IN PHASE ALTERNATION
DIVIDE VCLK BY 228 TO CREATE LINE PULSE FREQUENCY
CRYSTAL / MPU RATE / VSYNC RATE 14.218MHz / 889KHz / 49.97Hz 14.318MHz / 895KHz / 50.32Hz
KEYBOARD MATRIX DRIVE
HSYNC SIGNAL FOR REST OF SYSTEM
3us PULSE (APPROX)
OUTPUT LOW ON COUNT 0-15 LINE PULSE WIDTH = 4.5us
DC LEVEL ADJUST
DIVIDE BY 50
R73 PULLUP INDICATES DRAM IS ORGANISED IN 2 x 16K BANKS (PULLDOWN WOULD INDICATE 1 x 64K BANK)
A7 PULLDOWN PREVENTS WRITE TO SAM DURING RESET
KEYBOARD MATRIX RETURN
LEFT FIRE BUTTON
RIGHT FIRE BUTTON
ALTERNATING PHASE
FLYING RESISOR FITTED TO REDUCE COLOUR BLEED
SELECT LUMA SIGNAL FROM VDG OR EXTRA SYNCS FROM LINE PULSE CIRCUIT
MIX CHROMA & LUMA AMPLIFY / BUFFER
FS'
24 LINE DELAY
